Subjective-Reality-Labs/SD-001/hardware/battery_charger_devboard_multi/battery_charger_devboard_multi.kicad_sch

## KiCad design hardware/battery_charger_devboard_multi/battery_charger_devboard_multi.kicad_sch (2026-04-14)

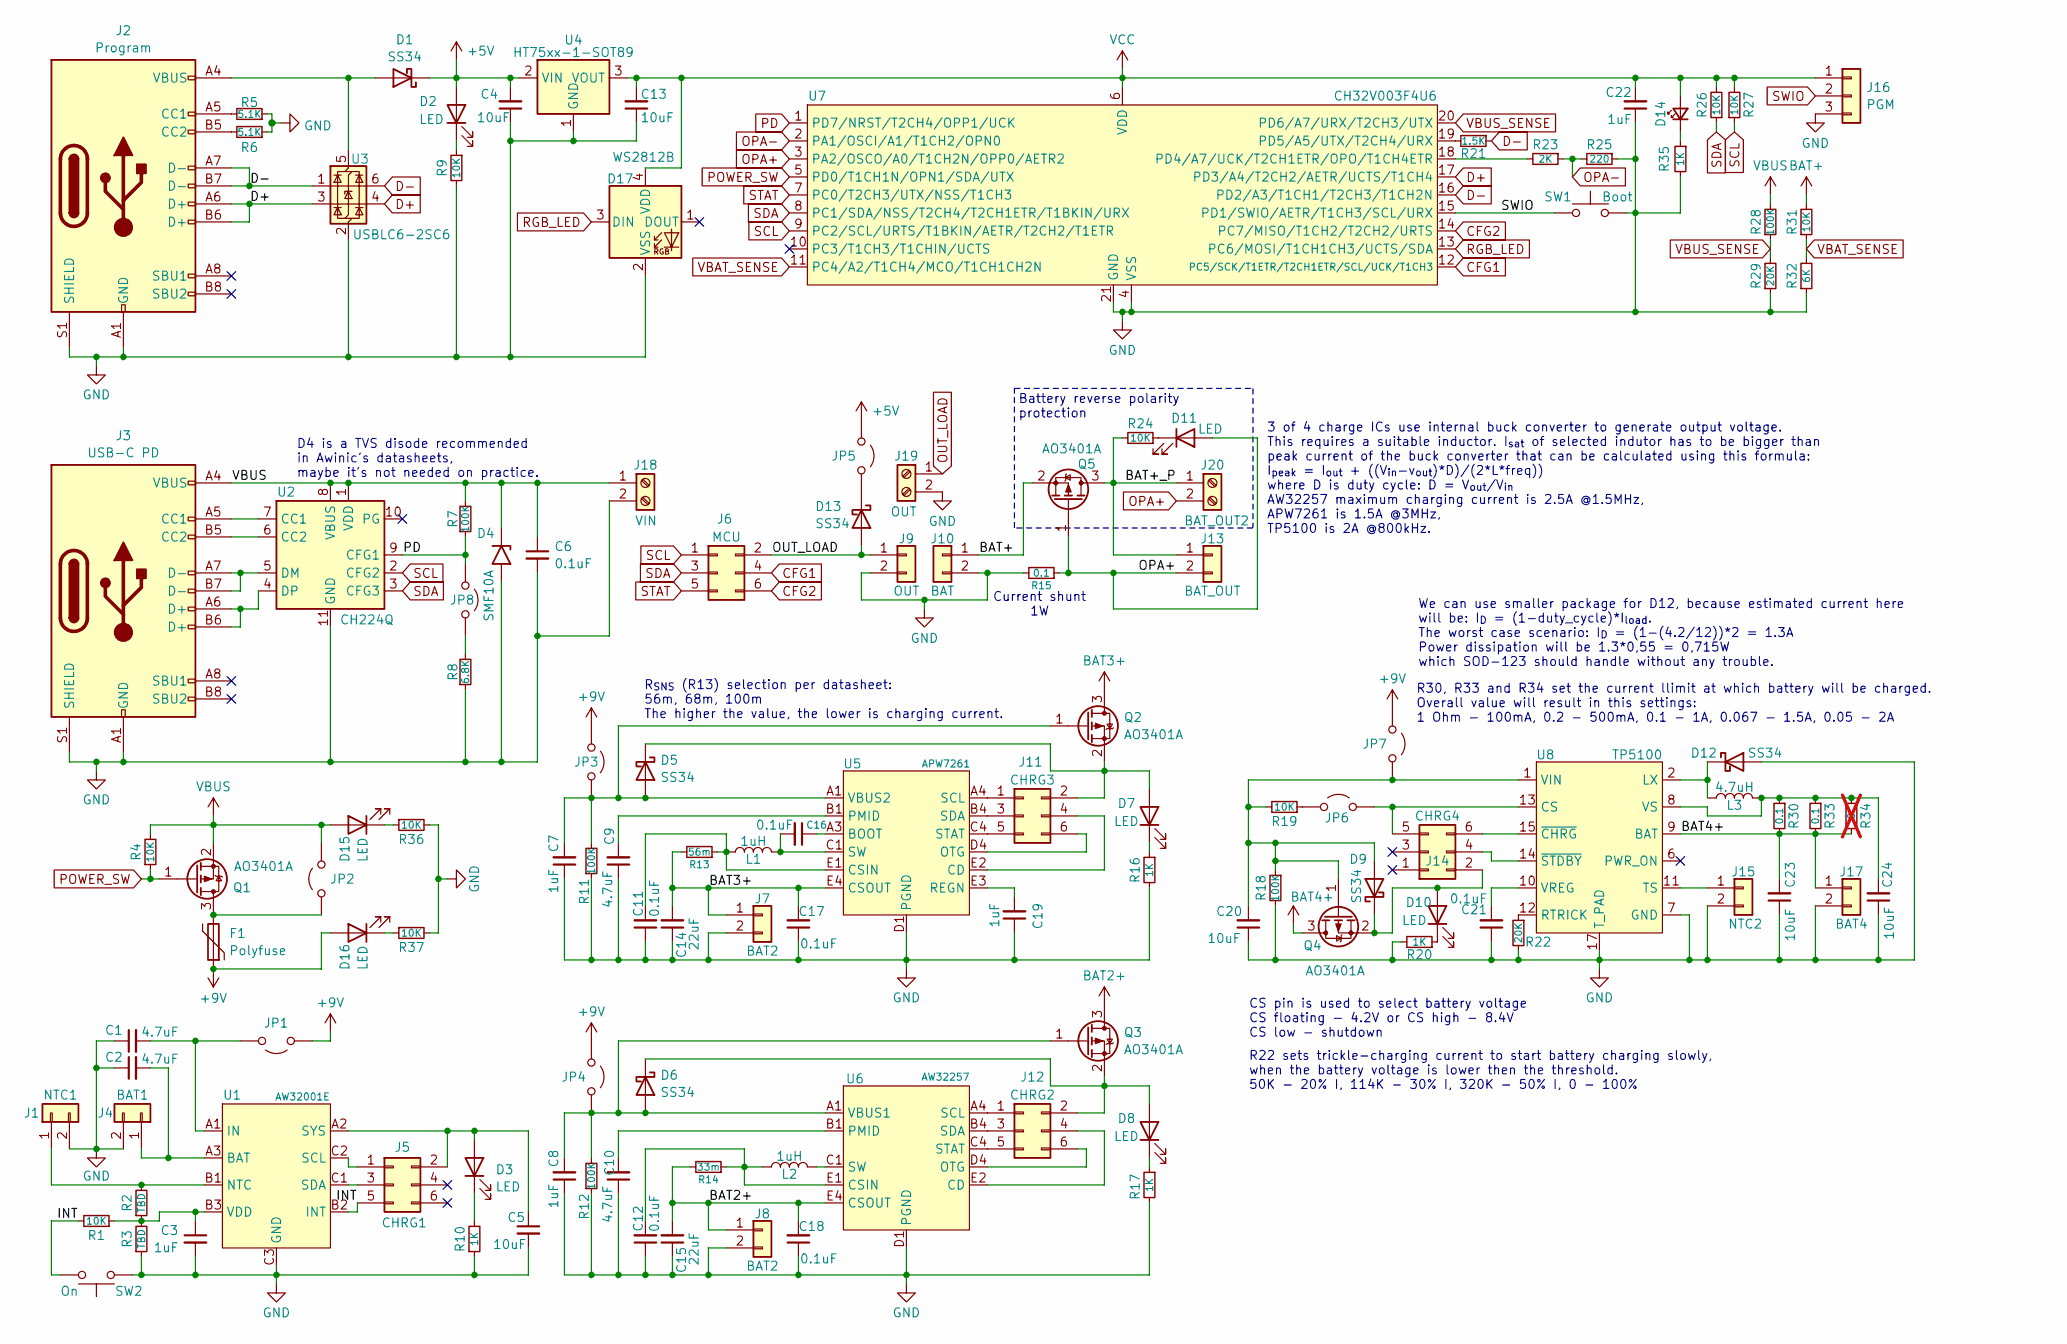
[picture p6: schematic battery_charger_devboard_multi.kicad_sch]

Parts:
C1, C2, C9, C10: 4.7uF; C_0603_1608Metric; LCSC C69335
C3, C7, C8, C19, C22: 1uF; C_0603_1608Metric; LCSC C59782
C4, C5, C13, C20, C23, C24: 10uF; C_0805_2012Metric; LCSC C95841
C6, C11, C12, C16, C17, C18, C21: 0.1uF; C_0603_1608Metric; LCSC C1590
C14, C15: 22uF; C_0805_2012Metric; LCSC C29277
D1, D5, D6, D9, D13: SS34; D_SMB; LCSC C266556
D2, D3, D7, D8, D10, D11, D14, D15, D16: LED; LED_0603_1608Metric
D4: SMF10A; D_SMF; LCSC C5353349
D12: SS34; D_SOD-123; LCSC C511866
D17: WS2812B; LED_WS2812B-1615_1.6x1.5mm; LCSC C41413180
F1: Polyfuse; Fuse_1812_4532Metric; LCSC C6851472
J1: NTC1; PinHeader_1x02_P2.54mm_Vertical
J2: Program; USB_C_Receptacle_GCT_USB4105-xx-A_16P_TopMnt_Horizontal
J3: USB-C PD; USB_C_Receptacle_GCT_USB4105-xx-A_16P_TopMnt_Horizontal; LCSC C393939
J4: BAT1; PinHeader_1x02_P2.54mm_Vertical
J5: CHRG1; PinHeader_2x03_P2.54mm_Vertical; LCSC C5383104
J6: MCU; PinHeader_2x03_P2.54mm_Vertical; LCSC C5383104
J7, J8: BAT2; PinHeader_1x02_P2.54mm_Vertical
J9: OUT; PinHeader_1x02_P2.54mm_Vertical
J10: BAT; PinHeader_1x02_P2.54mm_Vertical
J11: CHRG3; PinHeader_2x03_P2.54mm_Vertical; LCSC C5383104
J12: CHRG2; PinHeader_2x03_P2.54mm_Vertical; LCSC C5383104
J13: BAT_OUT; PinHeader_1x02_P2.54mm_Vertical
J14: CHRG4; PinHeader_2x03_P2.54mm_Vertical; LCSC C5383104
J15: NTC2; PinHeader_1x02_P2.54mm_Vertical
J16: PGM; PinHeader_1x03_P2.54mm_Vertical
J17: BAT4; PinHeader_1x02_P2.54mm_Vertical
J18: VIN; TerminalBlock_Phoenix_PT-1,5-2-3.5-H_1x02_P3.50mm_Horizontal; LCSC C466970
J19: OUT; TerminalBlock_Phoenix_PT-1,5-2-3.5-H_1x02_P3.50mm_Horizontal; LCSC C466970
J20: BAT_OUT2; TerminalBlock_Phoenix_PT-1,5-2-3.5-H_1x02_P3.50mm_Horizontal; LCSC C466970
JP1, JP2, JP3, JP4, JP5, JP6, JP7, JP8: Jumper_2_Open; PinHeader_1x02_P2.54mm_Vertical; LCSC C5274537
L1, L2: 1uH; L_1008_2520Metric; LCSC C5832356
L3: 4.7uH; L_1210_3225Metric; LCSC C17701271
Q1, Q2, Q3, Q4, Q5: AO3401A; SOT-23; LCSC C306862
R1, R4, R9, R19, R24, R26, R27, R31, R36, R37: 10K; R_0402_1005Metric; LCSC C60490
R2, R3: TBD; R_0603_1608Metric
R5, R6: 5.1K; R_0402_1005Metric; LCSC in-house
R7, R11, R12, R18, R28: 100K; R_0402_1005Metric; LCSC C60491
R8: 6.8K; R_0402_1005Metric; LCSC in-house
R10, R16, R17, R20, R35: 1K; R_0402_1005Metric; LCSC C106235
R13: 56m; R_0805_2012Metric; LCSC C172317
R14: 33m; R_0805_2012Metric; LCSC C859788
R15: 0.1; R_2512_6332Metric; LCSC C49164916
R21: 1.5K; R_0402_1005Metric; LCSC C60490
R22: 20K; R_0603_1608Metric; LCSC in-house
R23: 2K; R_0402_1005Metric; LCSC in-house
R25: 220; R_0402_1005Metric; LCSC C112291
R29: 20K; R_0402_1005Metric; LCSC in-house
R30, R33: 0.1; R_0805_2012Metric; LCSC C327057
R32: 6K; R_0402_1005Metric; LCSC C97819
R34: 0; R_0805_2012Metric; not fitted
SW1: Boot; SW_SPST_PTS810; LCSC C318904
SW2: On; SW_SPST_PTS810; LCSC C318904
U1: AW32001E; WLCSP1.68mm×1.68mm-9B; LCSC C5125890
U2: CH224Q; Texas_DSQ0010A_WSON-10-1EP_2x2mm_P0.4mm_EP0.9x1.5mm_Thermal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; LCSC C46061833
U3: USBLC6-2SC6; SOT-23-6; LCSC C5344574
U4: HT75xx-1-SOT89; SOT-89-3; LCSC C5296738
U5: APW7261; Anpec_WLCSP-20_1.76x2.03mm_Layout4x5_P0.4mm; LCSC# C691404
U6: AW32257; FCQFN_2×2-20L; LCSC# C5125876
U7: CH32V003F4U6; QFN-20-1EP_3x3mm_P0.4mm_EP1.65x1.65mm; LCSC C5299908
U8: TP5100; QFN-16-1EP_4x4mm_P0.5mm_EP2.45x2.45mm_ThermalVias; LCSC C379389

Connections:
+5V: C4.2, D1.1 (K), D2.2 (A), JP5.1 (A), U4.2 (VIN)
+9V: D16.2 (A), F1.1, JP1.1 (A), JP3.1 (A), JP4.1 (A), JP7.1 (A)
BAT2+: C15.2, C18.2, J8.1, Q3.3 (D), R14.2, U6.E4 (CSOUT)
BAT3+: C14.2, C17.2, J7.1, Q2.3 (D), R13.2, U5.E4 (CSOUT)
BAT4+: C23.2, J17.1, Q4.3 (D), R30.2, R33.2, R34.2, U8.9 (BAT)
BAT+: J10.1, Q5.2 (S), R31.2
BAT+_P: J13.1, J20.1, Q5.3 (D), R24.2
CFG1: J6.4, U7.12 (PC5/SCK/T1ETR/T2CH1ETR/SCL/UCK/T1CH3)
CFG2: J6.6, U7.14 (PC7/MISO/T1CH2/T2CH2/URTS)
D+: J2.A6 (D+), J2.B6 (D+), U3.3 (I/O2), U3.4 (I/O2), U7.17 (PD3/A4/T2CH2/AETR/UCTS/T1CH4)
D-: J2.A7 (D-), J2.B7 (D-), R21.1, U3.1 (I/O1), U3.6 (I/O1), U7.16 (PD2/A3/T1CH1/T2CH3/T1CH2N)
GND: C1.1, C2.1, C3.2, C4.1, C5.2, C6.2, C7.1, C8.1, C9.1, C10.1, C11.1, C12.1, C13.1, C14.1, C15.1, C17.1, C18.1, C19.1, C20.1, C21.1, C22.1, C23.1, C24.1, D4.2 (A2), D12.2 (A), D17.2 (VSS), J1.2, J2.A1 (GND), J2.A12 (GND), J2.B1 (GND), J2.B12 (GND), J2.S1 (SHIELD), J3.A1 (GND), J3.A12 (GND), J3.B1 (GND), J3.B12 (GND), J3.S1 (SHIELD), J4.2, J7.2, J8.2, J9.2, J10.2, J15.2, J16.3, J17.2, J18.2, J19.2, R3.1, R5.1, R6.1, R8.1, R9.2, R10.1, R11.1, R12.1, R15.2, R16.2, R17.2, R18.2, R20.2, R22.2, R25.1, R29.1, R32.1, R35.2, R36.2, R37.2, SW1.2, SW2.1, U1.C3 (GND), U2.11 (GND), U3.2 (GND), U4.1 (GND), U5.D1 (PGND), U5.D2 (PGND), U5.D3 (PGND), U6.D1 (PGND), U6.D2 (PGND), U6.D3 (PGND), U7.4 (VSS), U7.21 (GND), U8.7 (GND), U8.17 (T_PAD)
INT: J5.5, R1.2, SW2.2, U1.B2 (INT)
unnamed: C1.2, JP1.2 (B), U1.A1 (IN)
unnamed: C2.2, J4.1, U1.A3 (BAT)
unnamed: C3.1, R1.1, R2.1, R3.2, U1.B3 (VDD)
unnamed: C5.1, D3.2 (A), J5.2, U1.A2 (SYS)
unnamed: C7.2, D5.2 (A), JP3.2 (B), Q2.1 (G), R11.2, U5.A1 (VBUS2), U5.A2 (VBUS2)
unnamed: C8.2, D6.2 (A), JP4.2 (B), Q3.1 (G), R12.2, U6.A1 (VBUS1), U6.A2 (VBUS1)
unnamed: C9.2, U5.B1 (PMID), U5.B2 (PMID), U5.B3 (PMID)
unnamed: C10.2, U6.B1 (PMID), U6.B2 (PMID), U6.B3 (PMID)
unnamed: C11.2, L1.1, R13.1, U5.E1 (CSIN)
unnamed: C12.2, L2.1, R14.1, U6.E1 (CSIN)
unnamed: C16.1, U5.A3 (BOOT)
unnamed: C16.2, L1.2, U5.C1 (SW), U5.C2 (SW), U5.C3 (SW)
unnamed: C19.2, U5.E3 (REGN)
unnamed: C20.2, D9.2 (A), JP7.2 (B), Q4.1 (G), R18.1, R19.2, U8.1 (VIN), U8.4 (VIN), U8.5 (VIN), U8.16 (VIN)
unnamed: C21.2, U8.10 (VREG)
unnamed: C24.2, L3.2, R30.1, R33.1, R34.1, U8.8 (VS)
unnamed: D1.2 (A), J2.A4 (VBUS), J2.A9 (VBUS), J2.B4 (VBUS), J2.B9 (VBUS), U3.5 (VBUS)
unnamed: D2.1 (K), R9.1
unnamed: D3.1 (K), R10.2
unnamed: D5.1 (K), D7.2 (A), J11.2, Q2.2 (S)
unnamed: D6.1 (K), D8.2 (A), J12.2, Q3.2 (S)
unnamed: D7.1 (K), R16.1
unnamed: D8.1 (K), R17.1
unnamed: D10.1 (K), R20.1
unnamed: D9.1 (K), D10.2 (A), J14.2, Q4.2 (S)
unnamed: D11.1 (K), R24.1
unnamed: D12.1 (K), L3.1, U8.2 (LX), U8.3 (LX)
unnamed: D13.1 (K), JP5.2 (B)
unnamed: D14.1 (K), R35.1
unnamed: D15.1 (K), R36.1
unnamed: D16.1 (K), R37.1
unnamed: F1.2, JP2.1 (A), Q1.3 (D)
unnamed: J1.1, R2.2, U1.B1 (NTC)
unnamed: J2.A5 (CC1), R5.2
unnamed: J2.B5 (CC2), R6.2
unnamed: J3.A5 (CC1), U2.7 (CC1)
unnamed: J3.A6 (D+), J3.B6 (D+), U2.4 (DP)
unnamed: J3.A7 (D-), J3.B7 (D-), U2.5 (DM)
unnamed: J3.B5 (CC2), U2.6 (CC2)
unnamed: J5.1, U1.C2 (SCL)
unnamed: J5.3, U1.C1 (SDA)
unnamed: J11.1, U5.A4 (SCL)
unnamed: J11.3, U5.B4 (SDA)
unnamed: J11.4, U5.E2 (CD)
unnamed: J11.5, U5.C4 (STAT)
unnamed: J11.6, U5.D4 (OTG)
unnamed: J12.1, U6.A4 (SCL)
unnamed: J12.3, U6.B4 (SDA)
unnamed: J12.4, U6.E2 (CD)
unnamed: J12.5, U6.C4 (STAT)
unnamed: J12.6, U6.D4 (OTG)
unnamed: J14.4, U8.14 (~STDBY)
unnamed: J14.5, JP6.2 (B), U8.13 (CS)
unnamed: J14.6, U8.15 (~CHRG)
unnamed: J15.1, U8.11 (TS)
unnamed: JP6.1 (A), R19.1
unnamed: JP8.2 (B), R8.2
unnamed: L2.2, U6.C1 (SW), U6.C2 (SW), U6.C3 (SW)
unnamed: R21.2, U7.19 (PD5/A5/UTX/T2CH4/URX)
unnamed: R22.1, U8.12 (RTRICK)
unnamed: R23.2, U7.18 (PD4/A7/UCK/T2CH1ETR/OPO/T1CH4ETR)
OPA+: D11.2 (A), J13.2, J20.2, Q5.1 (G), R15.1, U7.3 (PA2/OSCO/A0/T1CH2N/OPP0/AETR2)
OPA-: R23.1, R25.2, U7.2 (PA1/OSCI/A1/T1CH2/OPN0)
OUT_LOAD: D13.2 (A), J6.2, J9.1, J19.1
PD: JP8.1 (A), R7.1, U2.9 (CFG1), U7.1 (PD7/NRST/T2CH4/OPP1/UCK)
POWER_SW: Q1.1 (G), R4.1, U7.5 (PD0/T1CH1N/OPN1/SDA/UTX)
RGB_LED: D17.3 (DIN), U7.13 (PC6/MOSI/T1CH1CH3/UCTS/SDA)
SCL: J6.1, R27.1, U2.2 (CFG2), U7.9 (PC2/SCL/URTS/T1BKIN/AETR/T2CH2/T1ETR)
SDA: J6.3, R26.1, U2.3 (CFG3), U7.8 (PC1/SDA/NSS/T2CH4/T2CH1ETR/T1BKIN/URX)
STAT: J6.5, U7.7 (PC0/T2CH3/UTX/NSS/T1CH3)
SWIO: J16.2, SW1.1, U7.15 (PD1/SWIO/AETR/T1CH3/SCL/URX)
VBAT_SENSE: R31.1, R32.2, U7.11 (PC4/A2/T1CH4/MCO/T1CH1CH2N)
VBUS: C6.1, D4.1 (A1), D15.2 (A), J3.A4 (VBUS), J3.A9 (VBUS), J3.B4 (VBUS), J3.B9 (VBUS), J18.1, JP2.2 (B), Q1.2 (S), R4.2, R7.2, R28.2, U2.1 (VDD), U2.8 (VBUS)
VBUS_SENSE: R28.1, R29.2, U7.20 (PD6/A7/URX/T2CH3/UTX)
VCC: C13.2, C22.2, D14.2 (A), D17.4 (VDD), J16.1, R26.2, R27.2, U4.3 (VOUT), U7.6 (VDD)

Notes on the sheet:
R_{SNS} (R13) selection per datasheet: 56m, 68m, 100m The higher the value, the lower is charging current.
D4 is a TVS disode recommended in Awinic's datasheets, maybe it's not needed on practice.
Battery reverse polarity protection
3 of 4 charge ICs use internal buck converter to generate output voltage. This requires a suitable inductor. I_{sat} of selected indutor has to be bigger than peak current of the buck converter that can be calculated using this formula: I_{peak} = I_{out} + ((V_{in}-v_{out})*D)/(2*L*freq)) where D 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
R22 sets trickle-charging current to start battery charging slowly, when the battery voltage is lower then the threshold. 50K - 20% I, 114K - 30% I, 320K - 50% I, 0 - 100%
R30, R33 and R34 set the current llimit at which battery will be charged. Overall value will result in this settings: 1 Ohm - 100mA, 0.2 - 500mA, 0.1 - 1A, 0.067 - 1.5A, 0.05 - 2A
Current shunt 1W
We can use smaller package for D12, because estimated current here will be: I_{D} = (1-duty_cycle)*I_{load}. The worst case scenario: I_{D} = (1-(4.2/12))*2 = 1.3A Power dissipation will be 1.3*0,55 = 0,715W which SOD-123 should handle without any trouble.
CS pin is used to select battery voltage CS floating - 4.2V or CS high - 8.4V CS low - shutdown
